CHAPARII/Chap-Split/images/Screenshot 2026-03-08 011443.png

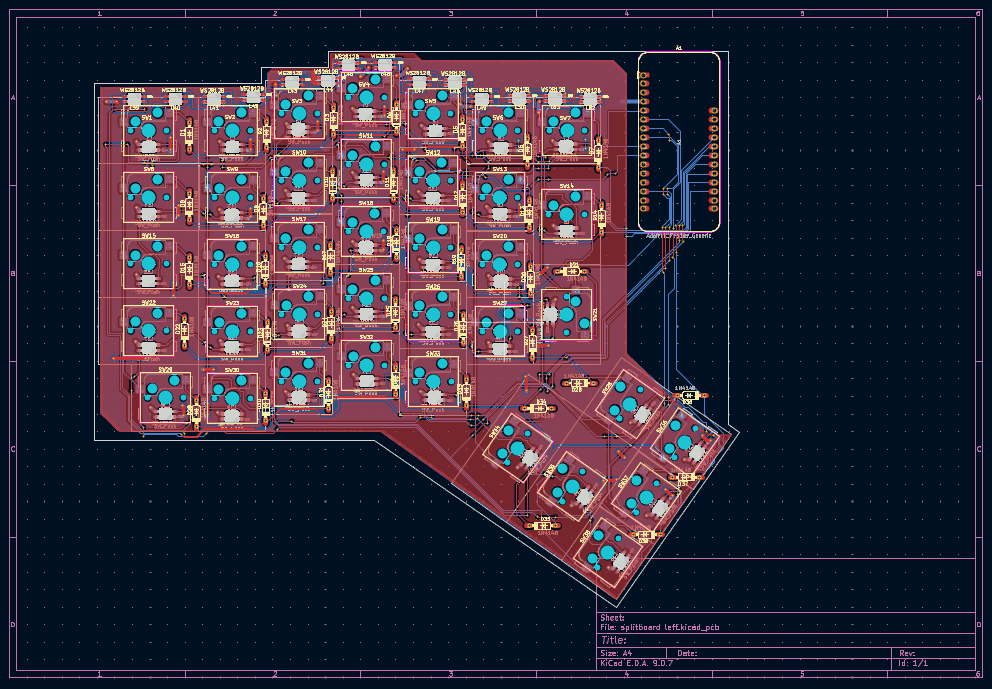
images/Screenshot 2026-03-08 011443.png
